JonathanFerron/BlueJay/build/arduino port from device manager.png

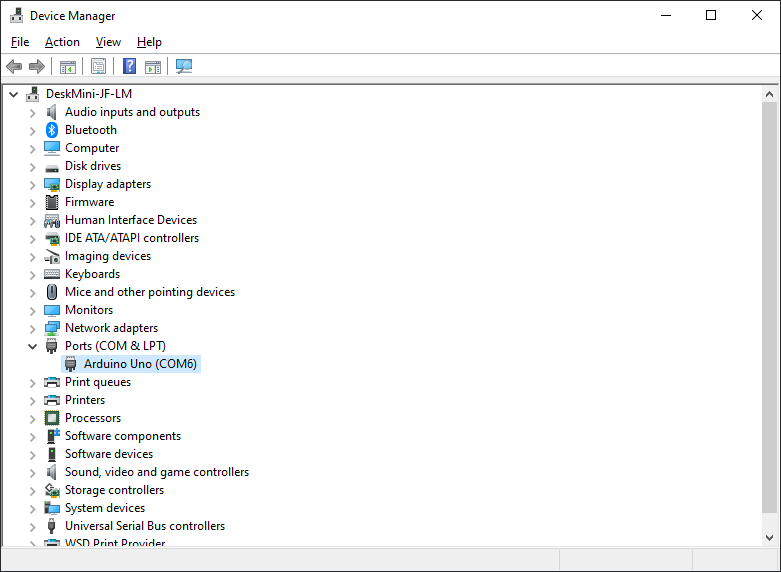
build/arduino port from device manager.png
