JonathanFerron/BlueJay/printouts/bluejay_left_3D_front.png

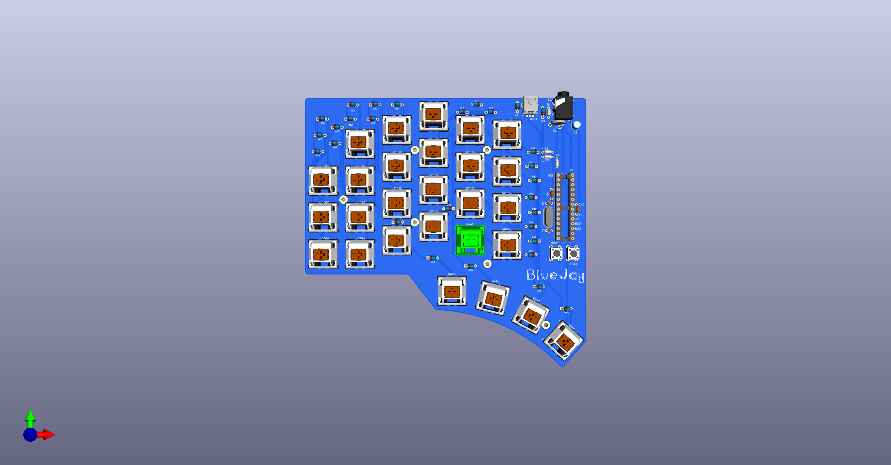
printouts/bluejay_left_3D_front.png
