JonathanFerron/BlueJay/printouts/bluejay_right_3D_back.png

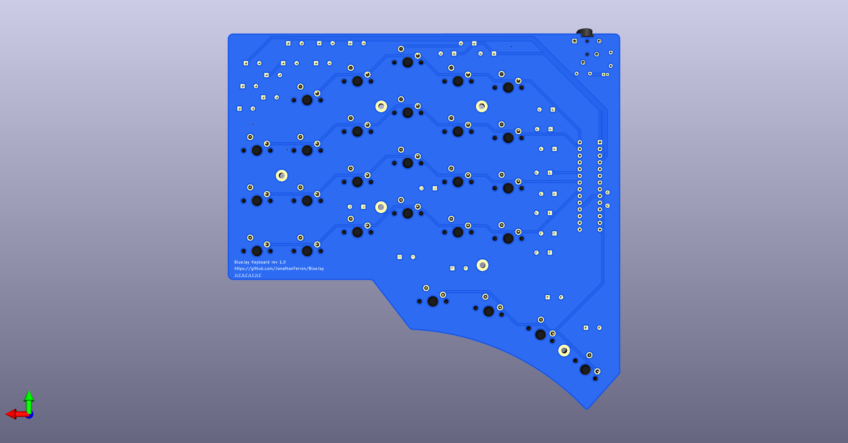
printouts/bluejay_right_3D_back.png
