JonathanFerron/BlueJay/printouts/bluejay_right_3D_front.png

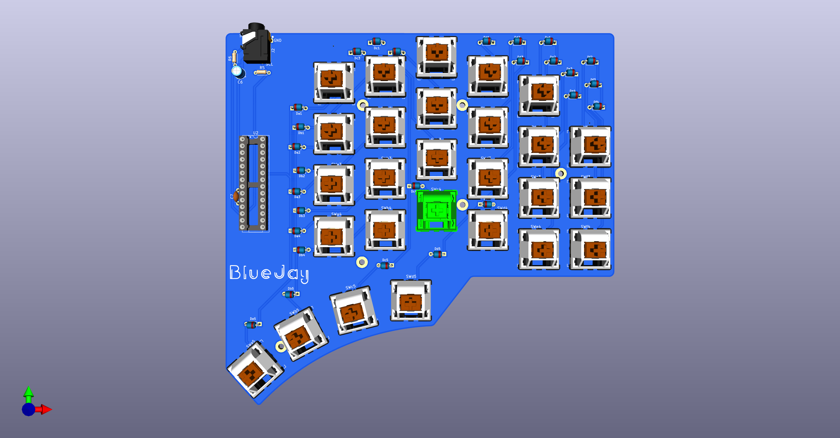
printouts/bluejay_right_3D_front.png
